lshachar/Something3D/extruder v2/extruder lever - straight V2.SLDPRT

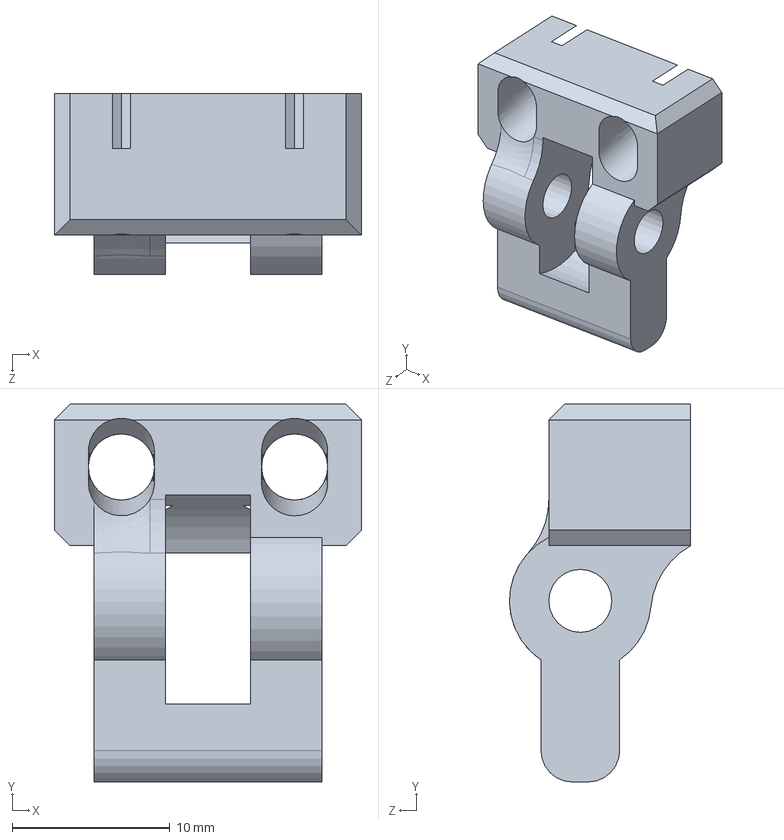
[picture p15: CAD file, 2021-02-14]
extruder v2/extruder lever - straight V2.SLDPRT
19.5 x 24.0 x 11.5 mm
