lshachar/Something3D/something3d fan mount/fan mount-cap.STL

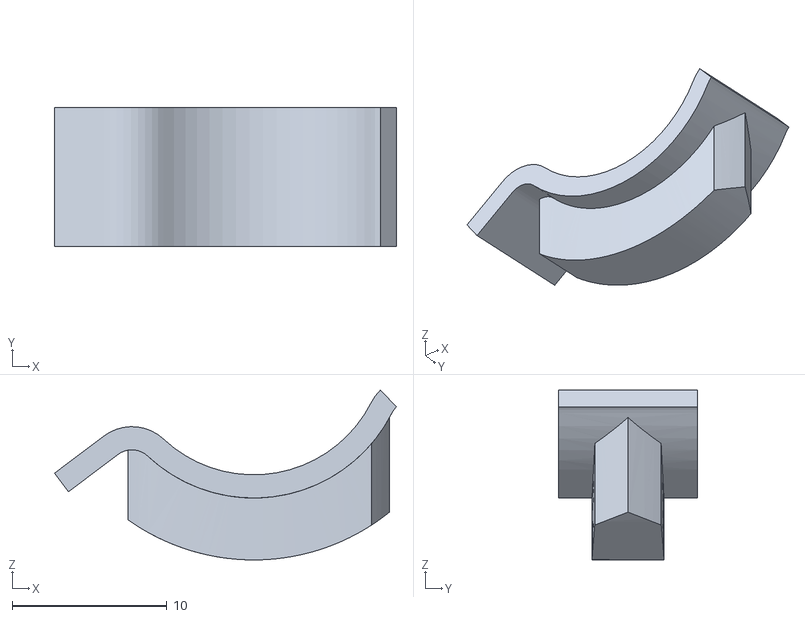
[picture p16: CAD file, 2021-02-14]
something3d fan mount/fan mount-cap.STL
22.1 x 9.00 x 11.0
