lshachar/Something3D/extruder v2/nema17 motor.SLDPRT

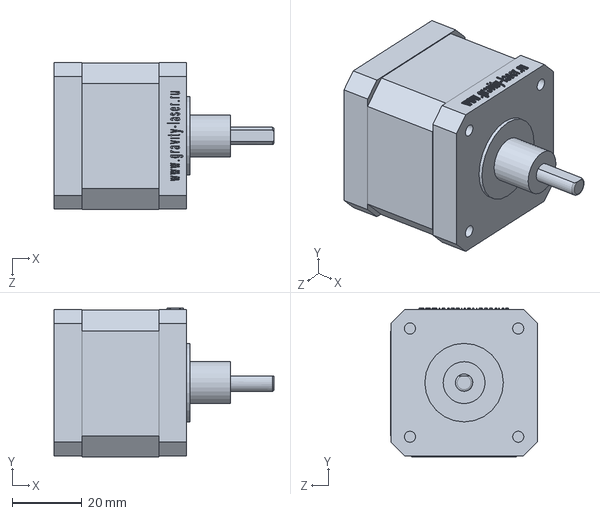
[picture p17: CAD file, 2021-02-14]
extruder v2/nema17 motor.SLDPRT
63.0 x 42.5 x 42.1 mm
