lshachar/Something3D/something3d fan mount/fan mount v2 - 3dprint.STL

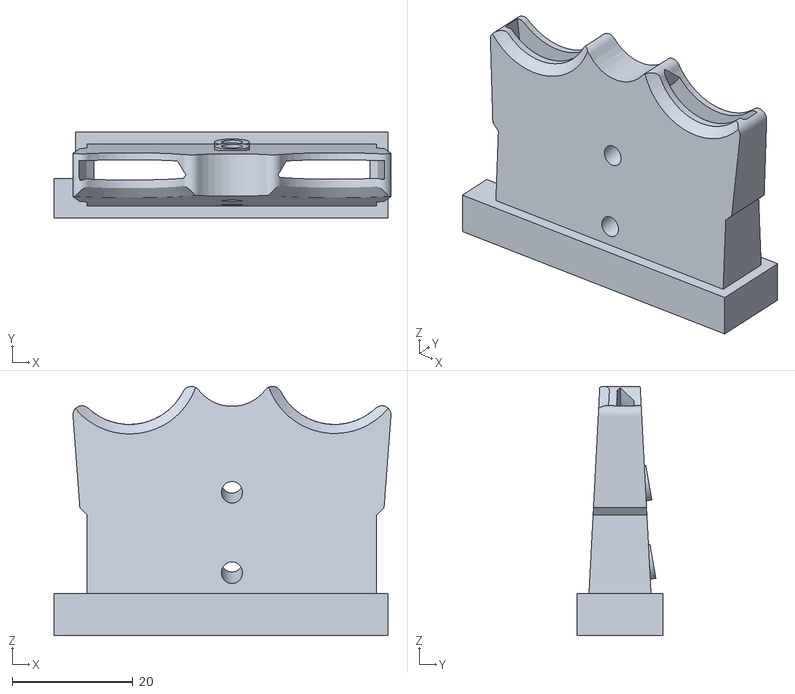
[picture p18: CAD file, 2021-02-14]
something3d fan mount/fan mount v2 - 3dprint.STL
55.9 x 14.3 x 41.3
