lshachar/Something3D/extruder v2/extruder lever - straight.SLDPRT

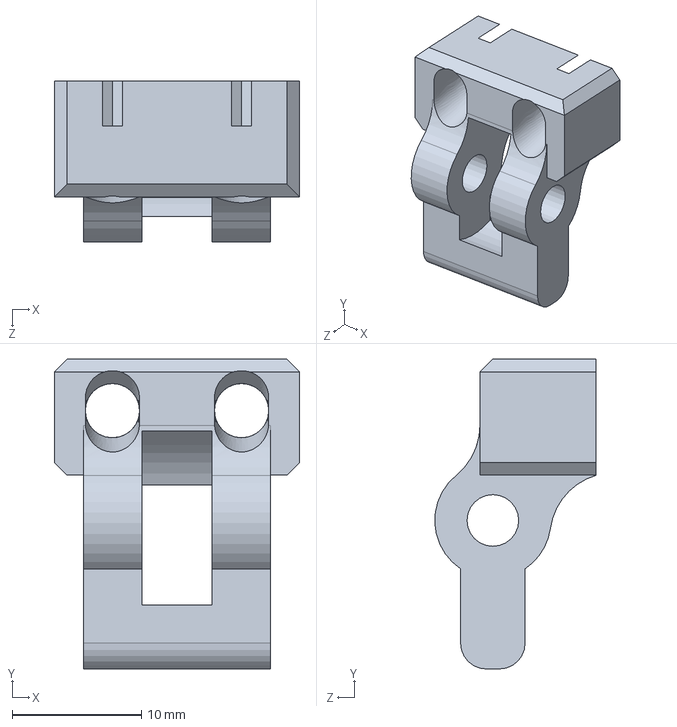
[picture p19: CAD file, 2021-02-14]
extruder v2/extruder lever - straight.SLDPRT
19.0 x 24.0 x 12.5 mm
