lshachar/Something3D/something3d fan mount/fan mount v2-fan mount support1 test.STL

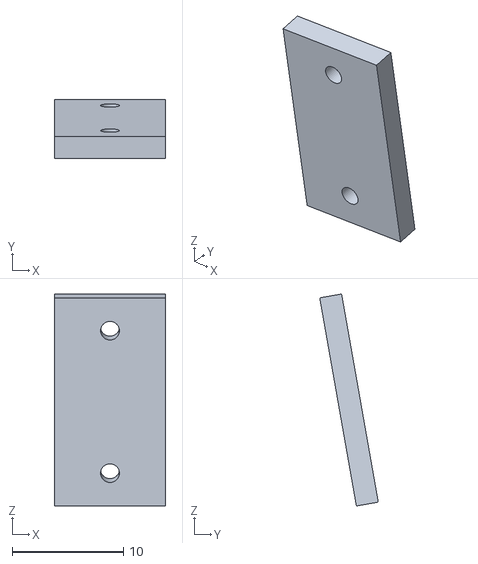
[picture p20: CAD file, 2021-02-14]
something3d fan mount/fan mount v2-fan mount support1 test.STL
10.0 x 5.27 x 19.1
