lshachar/Something3D/extruder v2/40x40x10 DC Fan.SLDPRT

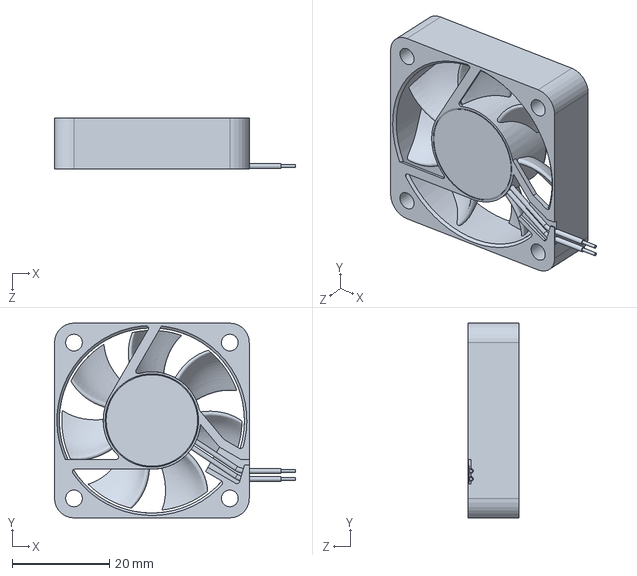
[picture p21: CAD file, 2021-02-14]
extruder v2/40x40x10 DC Fan.SLDPRT
49.5 x 40.0 x 10.5 mm
