lshachar/Something3D/something3d fan mount/bukoschnozzle-pla-fan-duct.SLDPRT

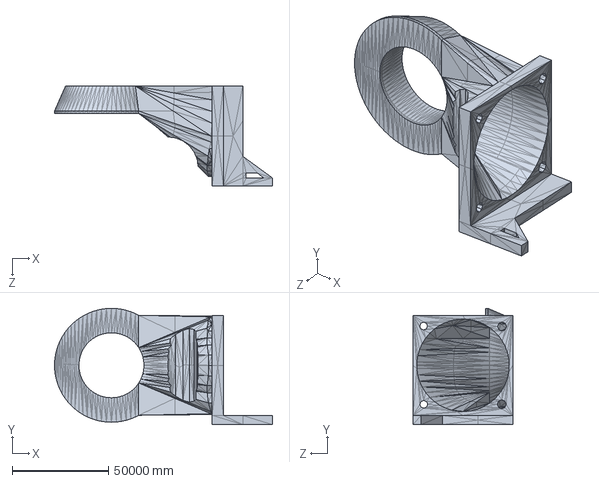
[picture p22: CAD file, 2021-02-14]
something3d fan mount/bukoschnozzle-pla-fan-duct.SLDPRT
113404.0 x 60502.0 x 52002.0 mm
