lshachar/Something3D/something3d fan mount/fan mount-test.STL

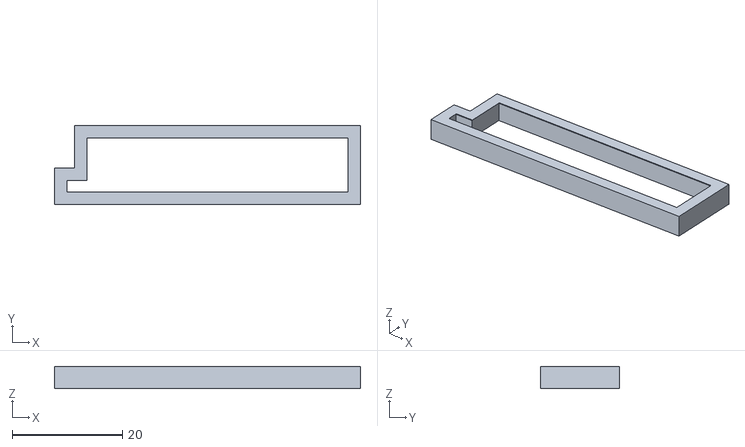
[picture p23: CAD file, 2021-02-14]
something3d fan mount/fan mount-test.STL
55.4 x 14.3 x 4.00
