lshachar/Something3D/something3d fan mount/fan mount v2-fan mount support2 test.STL

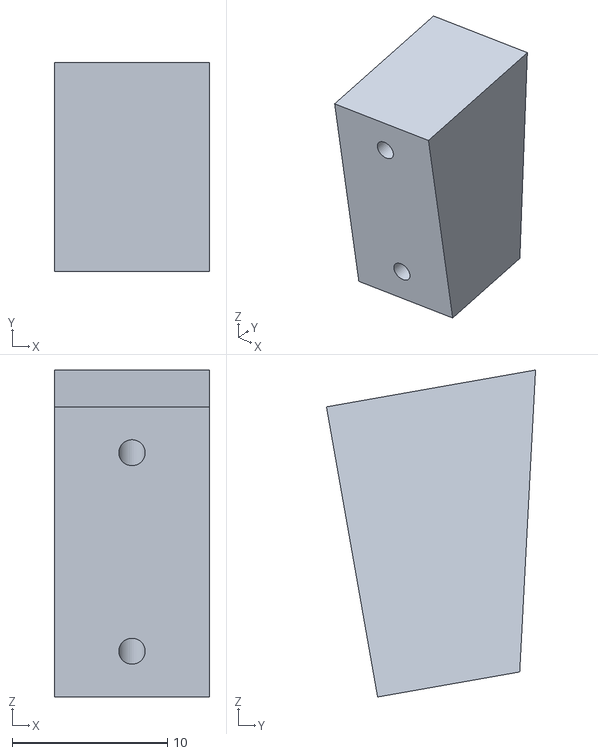
[picture p24: CAD file, 2021-02-14]
something3d fan mount/fan mount v2-fan mount support2 test.STL
10.0 x 13.5 x 21.1
