lshachar/Something3D/something3d fan mount/fan mount v2-support - 3dprint.STL

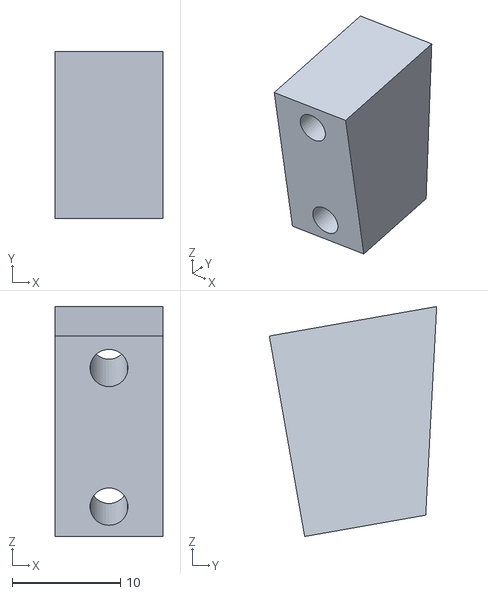
[picture p25: CAD file, 2021-02-14]
something3d fan mount/fan mount v2-support - 3dprint.STL
10.0 x 15.5 x 21.2
